jaxonteague/business-card/microcontroller/business card/Core/Inc/main.h

#define Button_Pin GPIO_PIN_4
#define Button_GPIO_Port GPIOA
#define Button_EXTI_IRQn EXTI4_15_IRQn
#define Led_Data_Pin GPIO_PIN_7
#define Led_Data_GPIO_Port GPIOA
